pdaehne/XUM1541-Pro-Micro/images/Resistor_Network_RN1.jpg

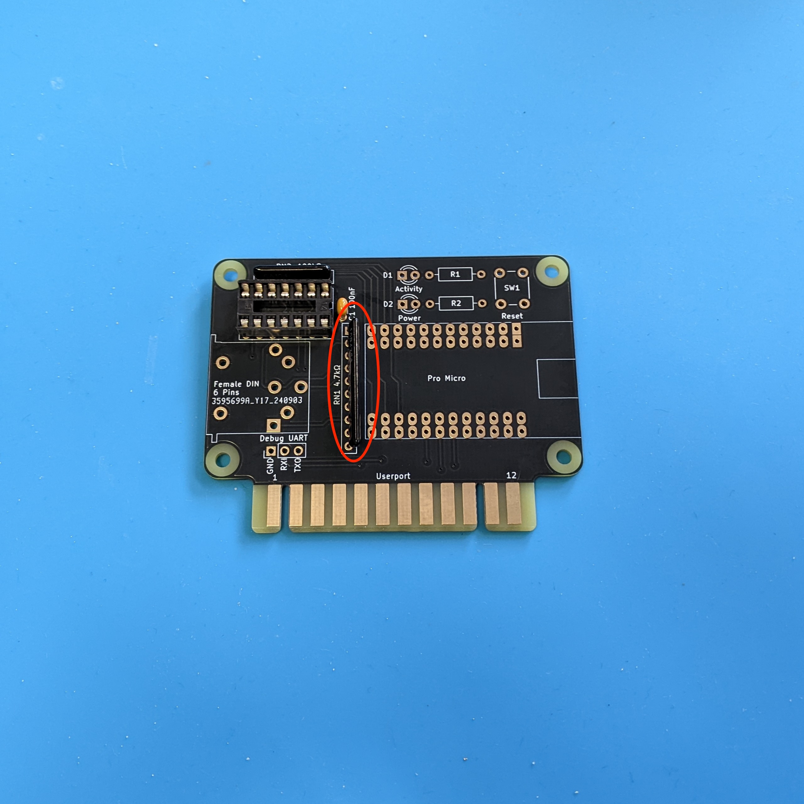
images/Resistor_Network_RN1.jpg
